MakersAsylumIndia/MAPone/datasheets/2EZ13D5-TP_sml.jpg

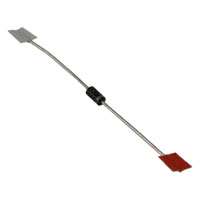
datasheets/2EZ13D5-TP_sml.jpg
