MakersAsylumIndia/MAPone/datasheets/9B-SERIES_sml.jpg

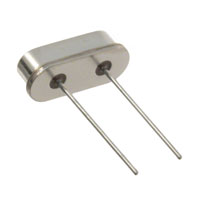
datasheets/9B-SERIES_sml.jpg
