MakersAsylumIndia/MAPone/datasheets/28-PDip_sml.jpg

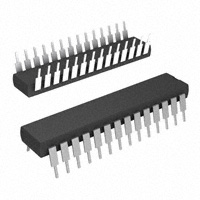
datasheets/28-PDip_sml.jpg
