MakersAsylumIndia/MAPone/datasheets/28-VFQFN Exposed Pad_sml.jpg

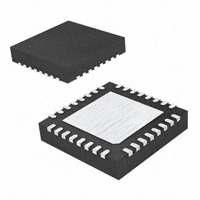
datasheets/28-VFQFN Exposed Pad_sml.jpg
