MakersAsylumIndia/MAPone/datasheets/67996-206hlf_sml.JPG

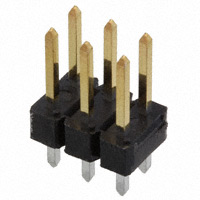
datasheets/67996-206hlf_sml.JPG
