MakersAsylumIndia/MAPone/datasheets/10118193-0001LF_sml.jpg

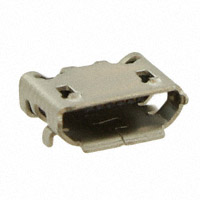
datasheets/10118193-0001LF_sml.jpg
