MakersAsylumIndia/MAPone/datasheets/CF Series 10k_sml.jpg

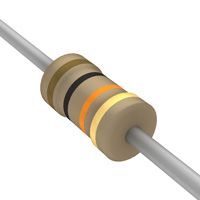
datasheets/CF Series 10k_sml.jpg
