MakersAsylumIndia/MAPone/datasheets/CL Series 0805(2012 Metric) 9_sml.jpg

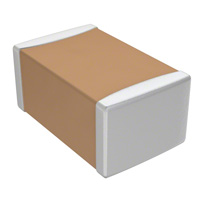
datasheets/CL Series 0805(2012 Metric) 9_sml.jpg
