MakersAsylumIndia/MAPone/datasheets/ED281DT_sml.JPG

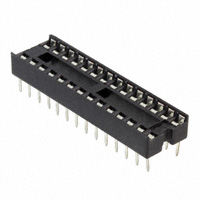
datasheets/ED281DT_sml.JPG
