MakersAsylumIndia/MAPone/datasheets/ERJ-0805 Pkg_sml.jpg

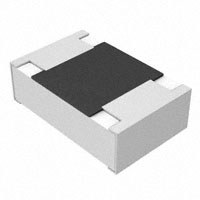
datasheets/ERJ-0805 Pkg_sml.jpg
