MakersAsylumIndia/MAPone/datasheets/ESK107M035AE3AA_sml.jpg

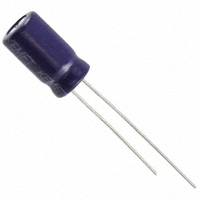
datasheets/ESK107M035AE3AA_sml.jpg
