MakersAsylumIndia/MAPone/datasheets/FSM4JH_sml.jpg

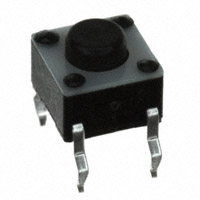
datasheets/FSM4JH_sml.jpg
