MakersAsylumIndia/MAPone/datasheets/LTST-C170YKT,LTST-C170CKT,LTST-C170AKT,LTST-C170EKT,LTST-C170GKT_sml.jpg

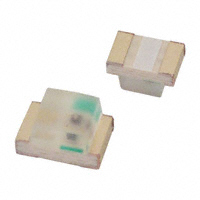
datasheets/LTST-C170YKT,LTST-C170CKT,LTST-C170AKT,LTST-C170EKT,LTST-C170GKT_sml.jpg
