MakersAsylumIndia/MAPone/datasheets/MFG_RMC SERIES_sml.jpg

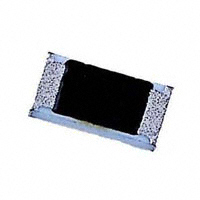
datasheets/MFG_RMC SERIES_sml.jpg
