MakersAsylumIndia/MAPone/datasheets/PJ-002A_sml.jpg

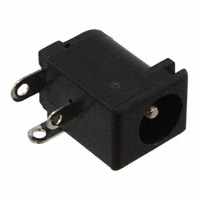
datasheets/PJ-002A_sml.jpg
