MakersAsylumIndia/MAPone/datasheets/PPPC061LGBN-RC_sml (1).jpg

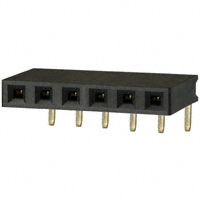
datasheets/PPPC061LGBN-RC_sml (1).jpg
