MakersAsylumIndia/MAPone/datasheets/PPTC061LFBN-RC_sml.jpg

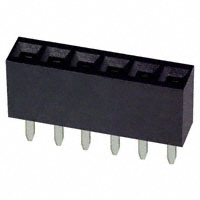
datasheets/PPTC061LFBN-RC_sml.jpg
