MakersAsylumIndia/MAPone/datasheets/PPTC081LFBN-RC_sml.jpg

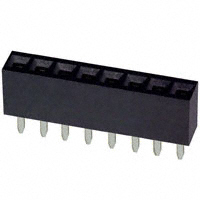
datasheets/PPTC081LFBN-RC_sml.jpg
