MakersAsylumIndia/MAPone/datasheets/PREC040SAAN-RC_sml.jpg

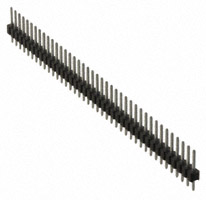
datasheets/PREC040SAAN-RC_sml.jpg
