MakersAsylumIndia/MAPone/datasheets/SOT-23-6 PKG_sml.jpg

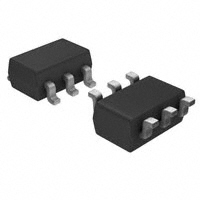
datasheets/SOT-23-6 PKG_sml.jpg
