MakersAsylumIndia/MAPone/datasheets/TO-220-3_sml.jpg

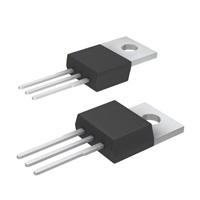
datasheets/TO-220-3_sml.jpg
