MakersAsylumIndia/MAPone/datasheets/WP710A10GD_sml.jpg

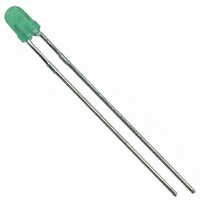
datasheets/WP710A10GD_sml.jpg
