MakersAsylumIndia/MAPone/images/DSC_0109.jpg

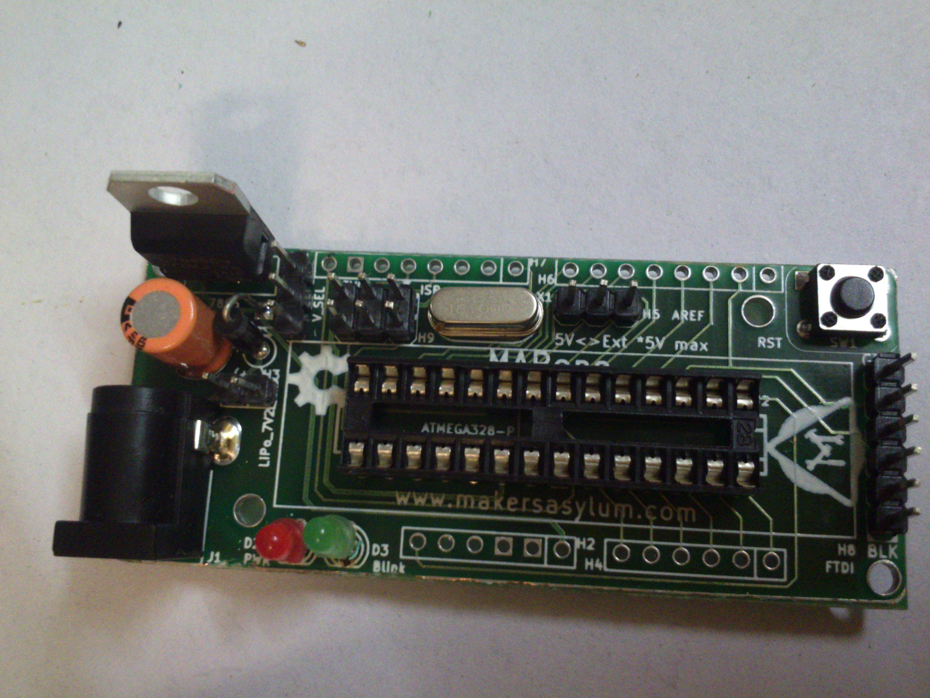
images/DSC_0109.jpg
