MakersAsylumIndia/MAPone/images/DSCN0591.JPG

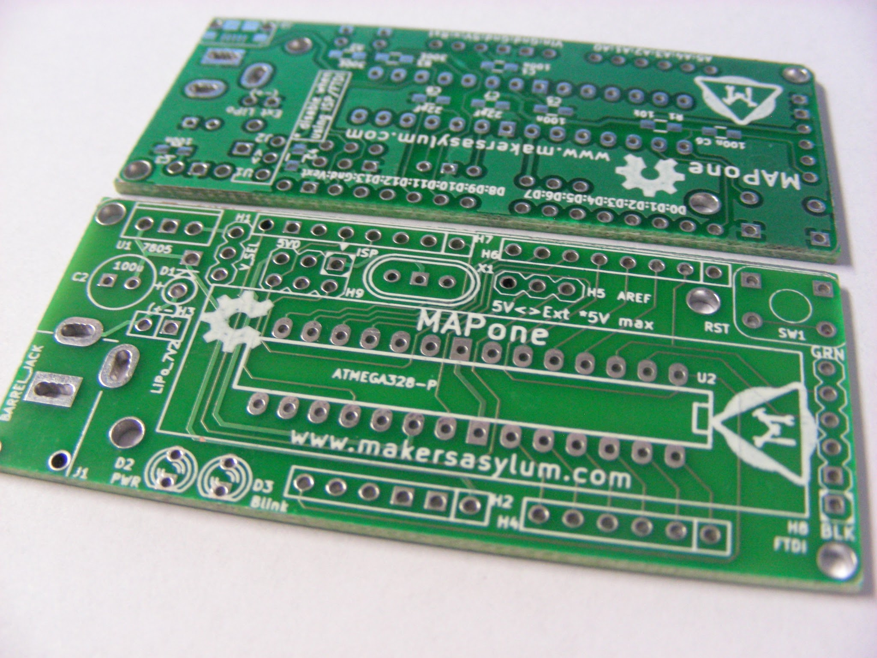
images/DSCN0591.JPG
