MakersAsylumIndia/MAPone/images/MAPone_01.png

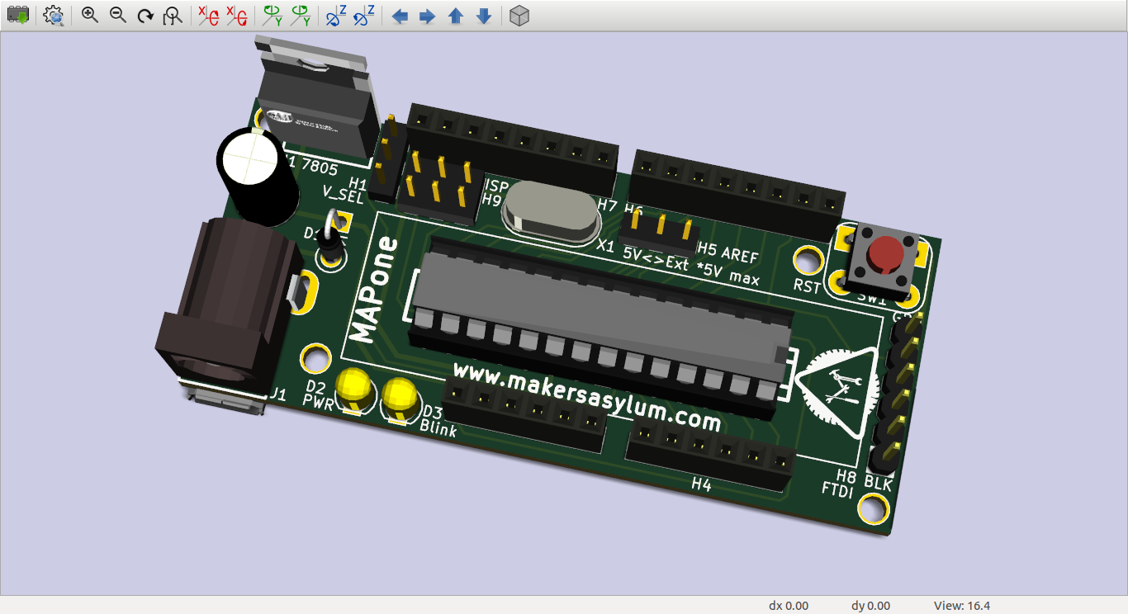
images/MAPone_01.png
