MakersAsylumIndia/MAPone/images/MAPone_02.png

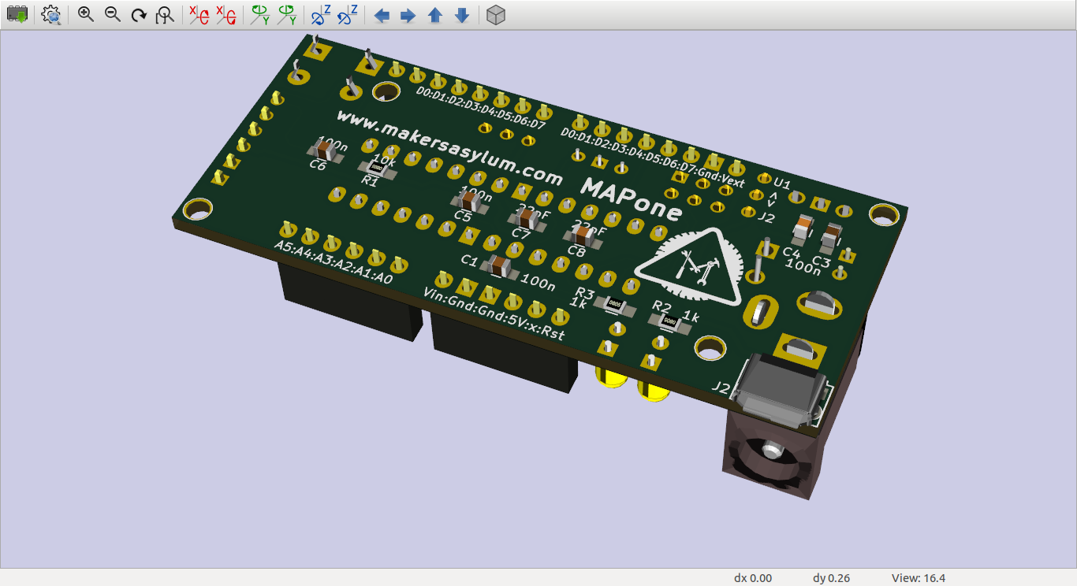
images/MAPone_02.png
