MakersAsylumIndia/MAPone/images/MAPone_03.png

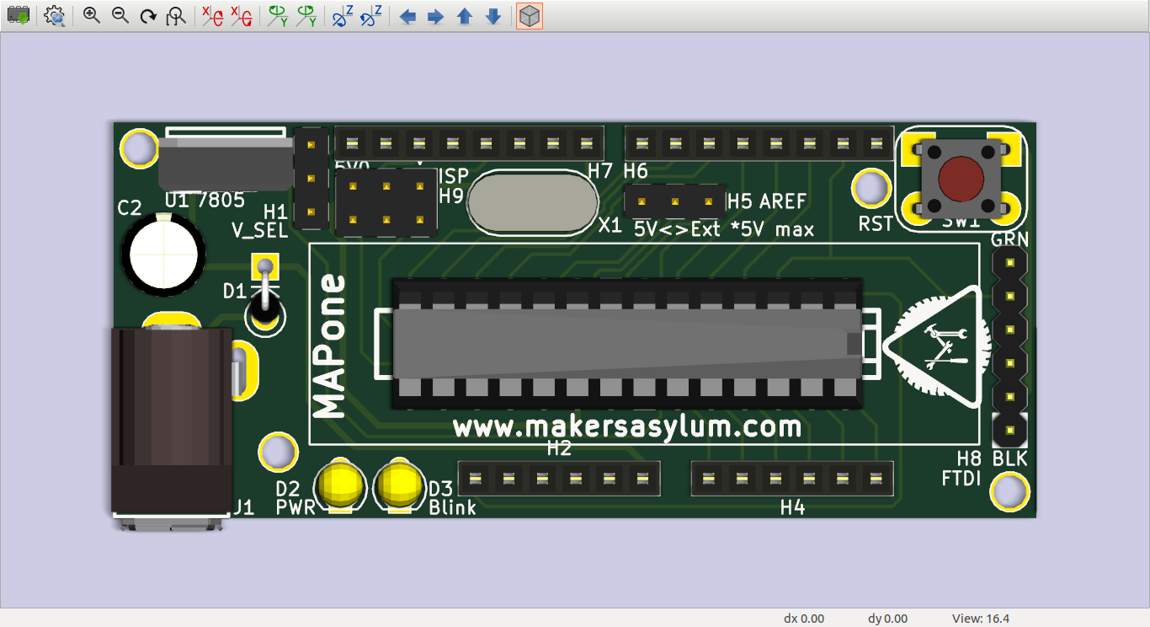
images/MAPone_03.png
