MakersAsylumIndia/MAPone/images/MAPone_04.png

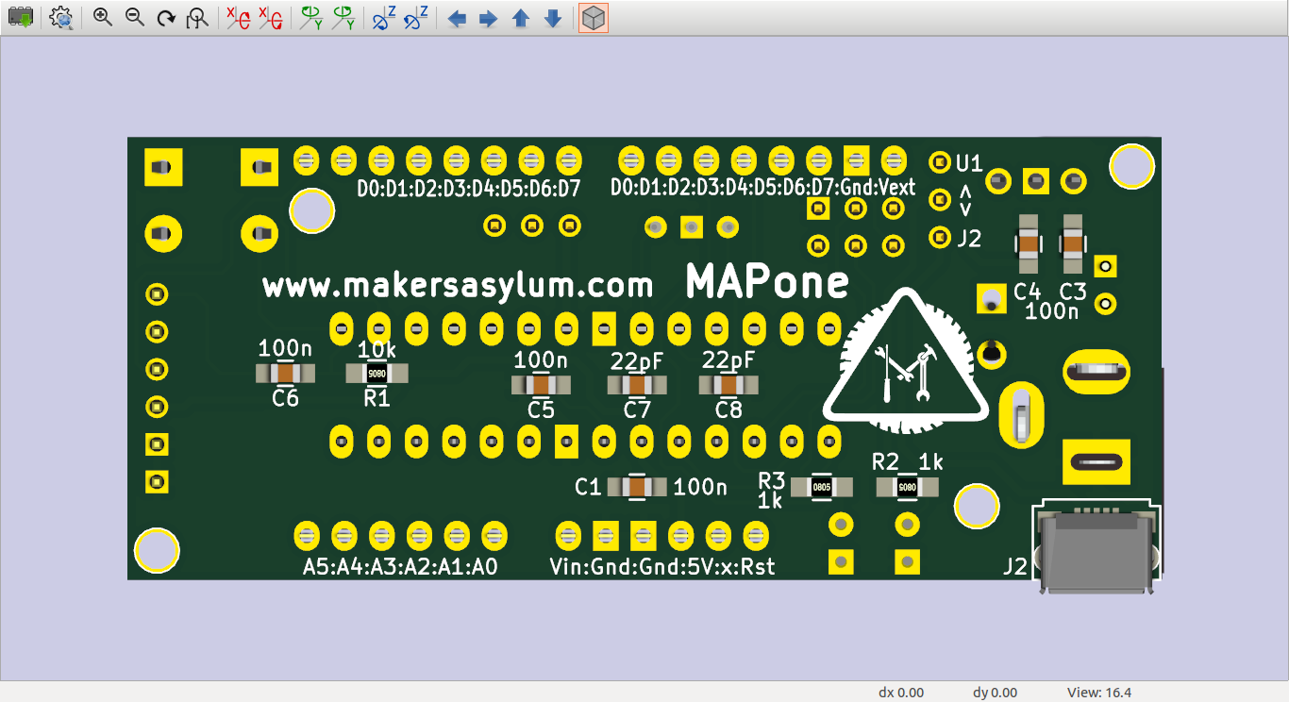
images/MAPone_04.png
