MakersAsylumIndia/MAPone/images/MAPone_08.png

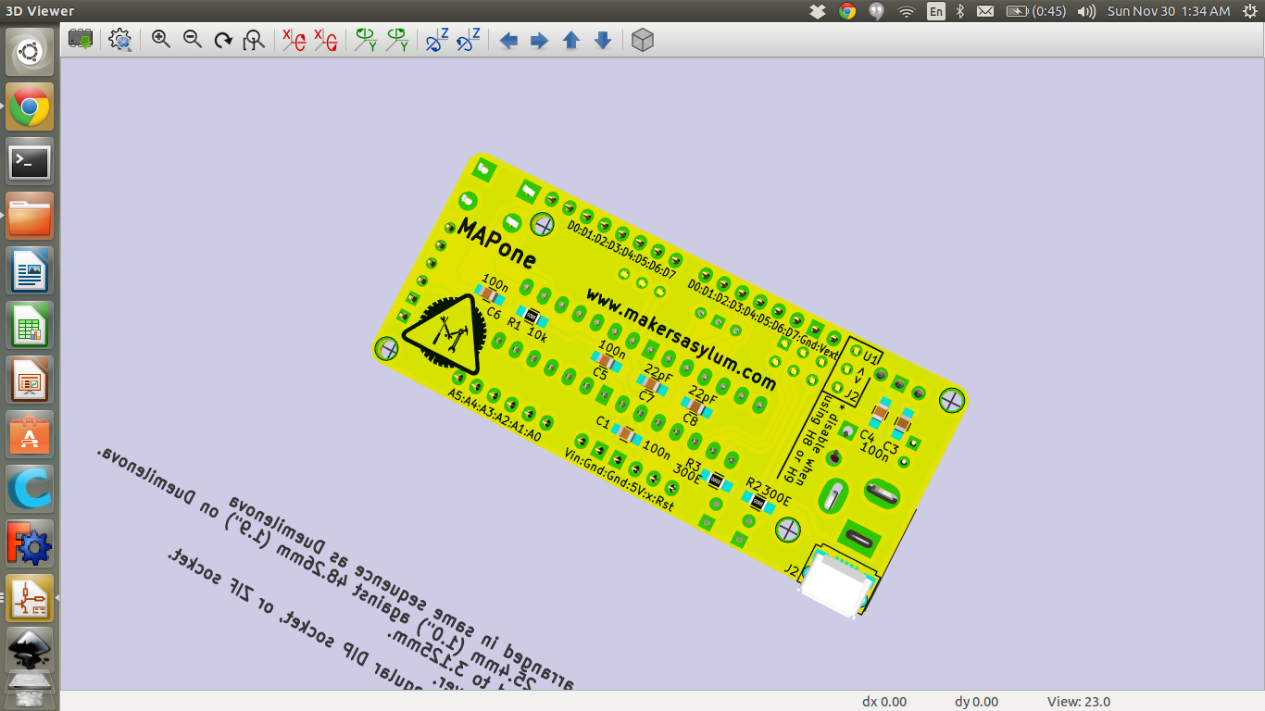
images/MAPone_08.png
