MakersAsylumIndia/MAPone/images/MAPone_09.png

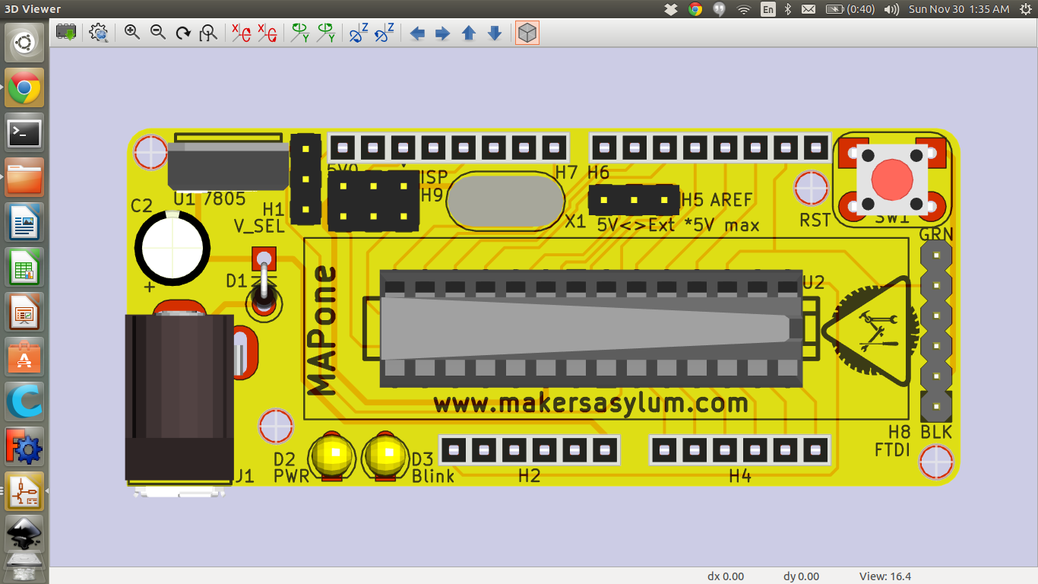
images/MAPone_09.png
