MakersAsylumIndia/MAPone/images/MAPone_10.png

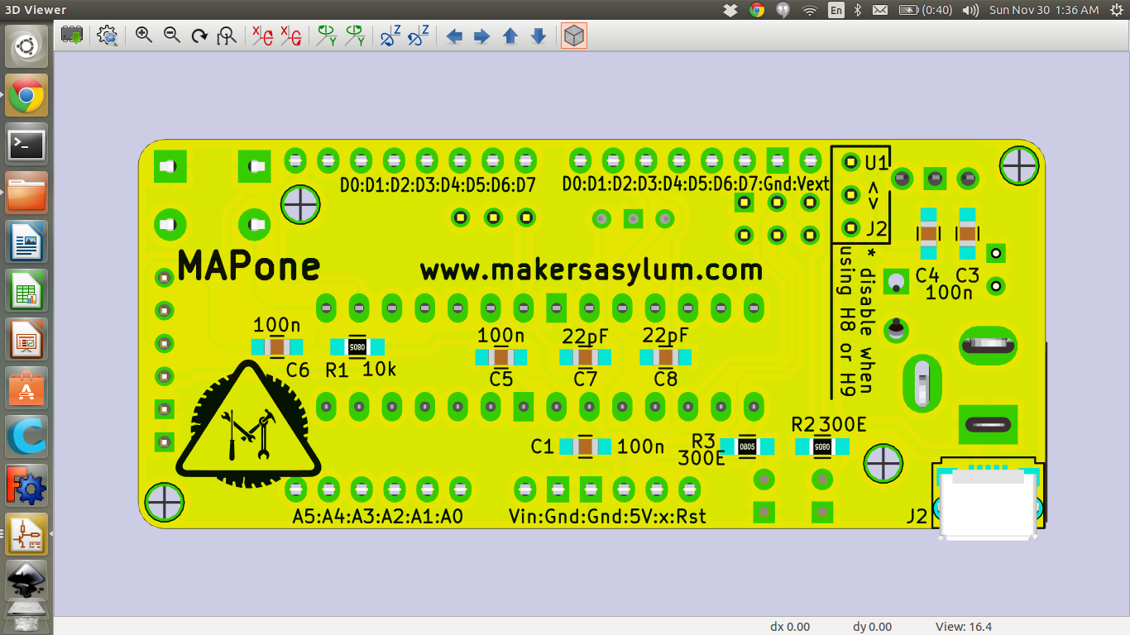
images/MAPone_10.png
