MakersAsylumIndia/MAPone/images/MAPone_13.png

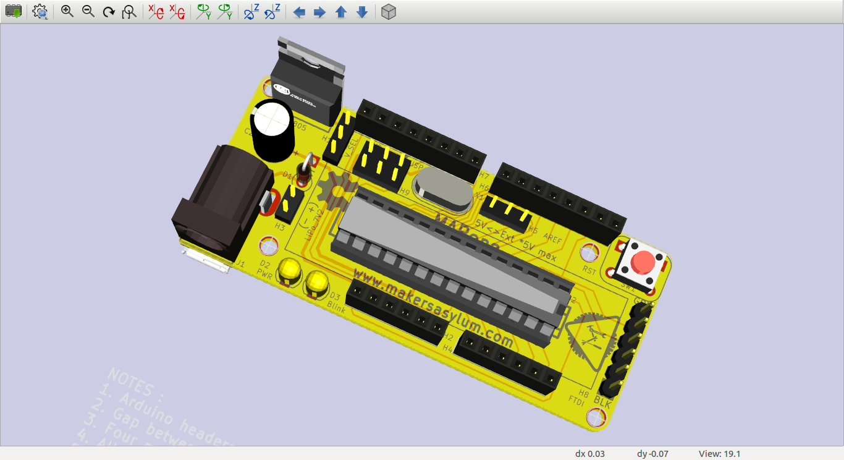
images/MAPone_13.png
