MakersAsylumIndia/MAPone/images/MAPone_14.png

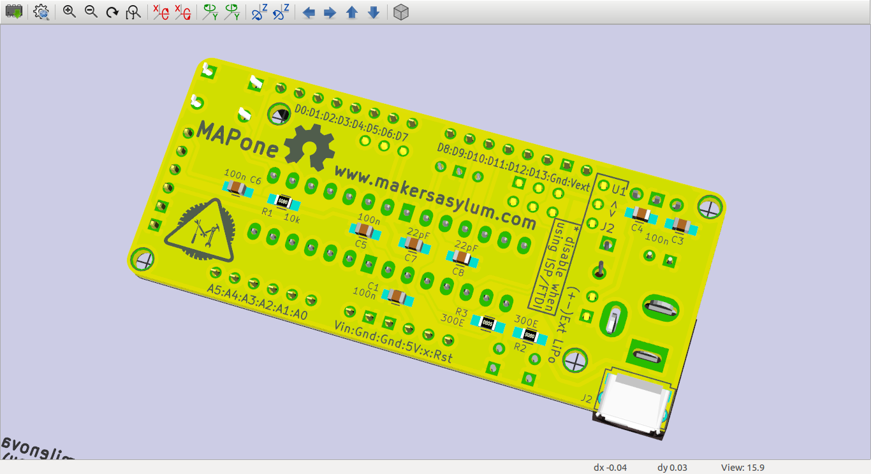
images/MAPone_14.png
