MakersAsylumIndia/MAPone/images/MAPone_15.png

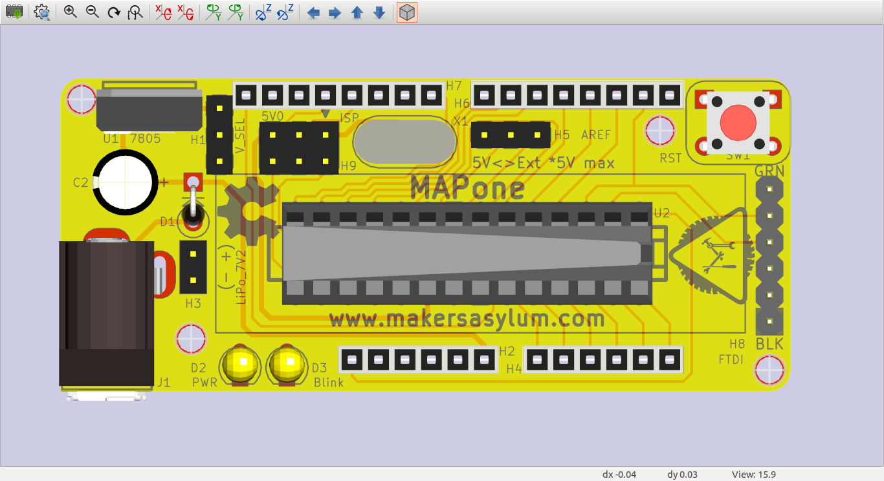
images/MAPone_15.png
