MakersAsylumIndia/MAPone/images/MAPone_16.png

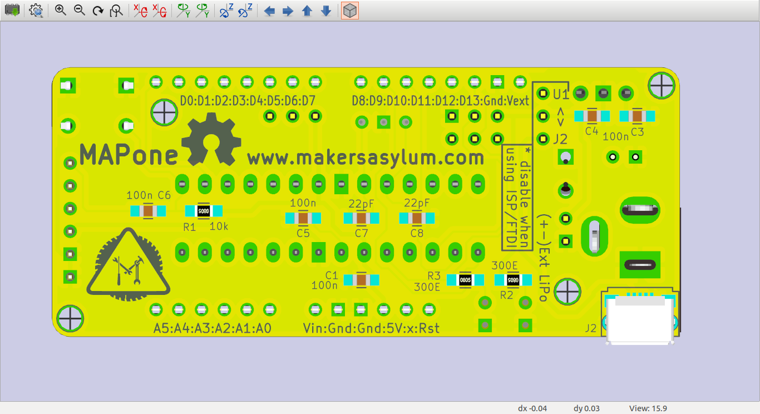
images/MAPone_16.png
