MakersAsylumIndia/MAPone/images/MAPone_18.png

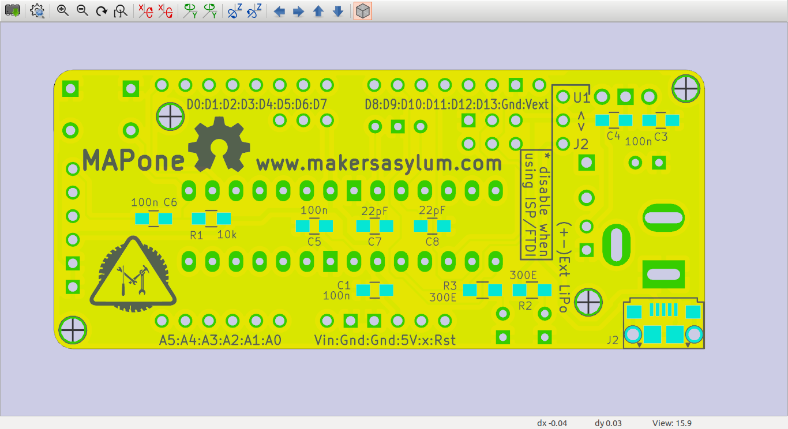
images/MAPone_18.png
