MakersAsylumIndia/MAPone/images/MAPone_19.png

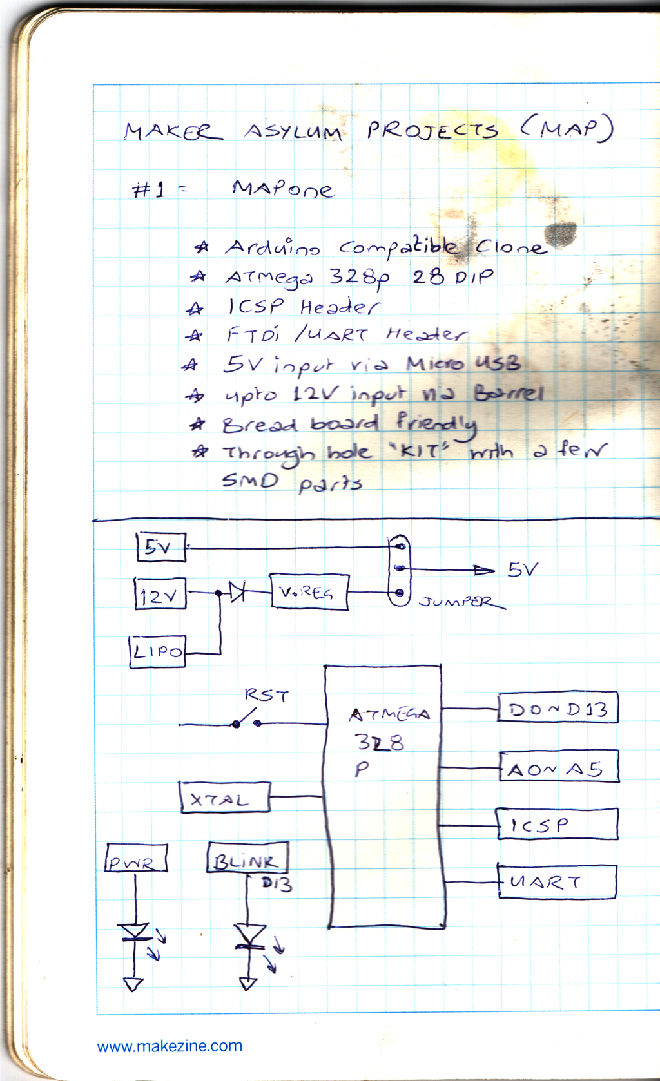
images/MAPone_19.png
