MakersAsylumIndia/MAPone/kicad/MAPone_assembly.png

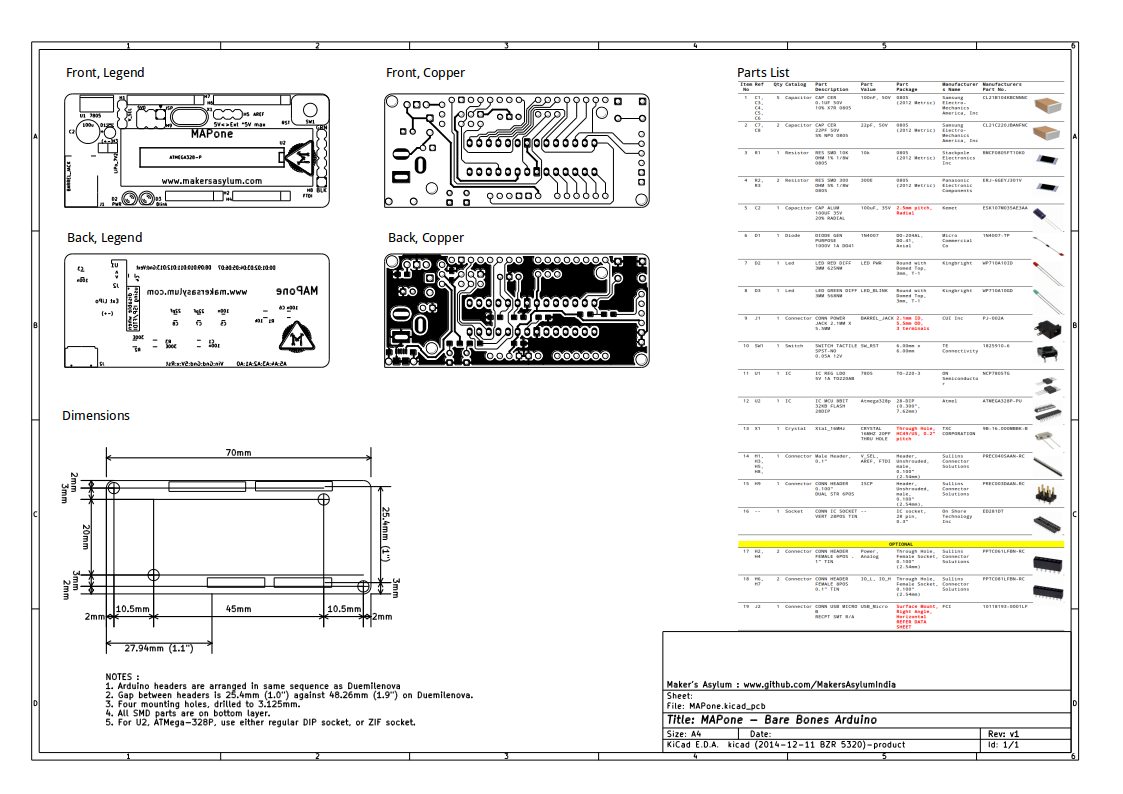
kicad/MAPone_assembly.png
