MakersAsylumIndia/MAPone/Eagle/USB-UART Bridge/UsbUartBridge.sch

## EAGLE design Eagle/USB-UART Bridge/UsbUartBridge.sch (2014-12-02)

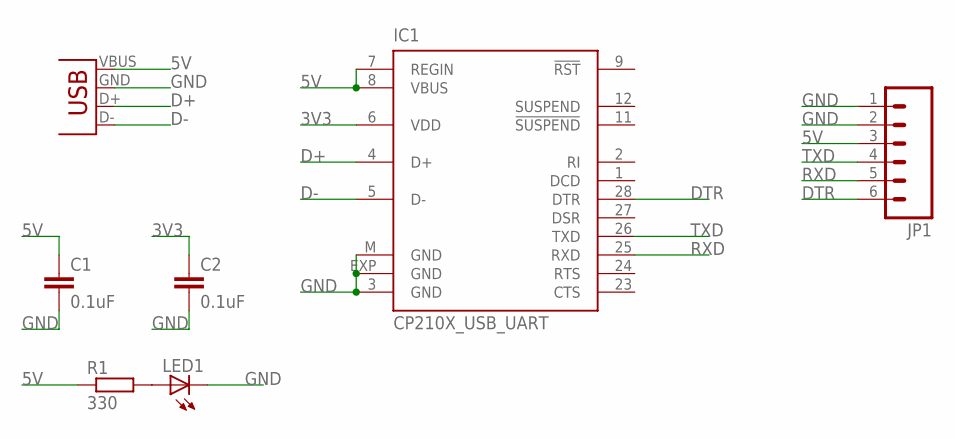
[picture p56: schematic UsbUartBridge.sch]

Parts:
C1, C2: 0.1uF; C025-024X044
IC1: CP210X_USB_UART; MLP28
JP1: M06SIP; 1X06
LED1: LED3MM
R1: 330; 0204/7
X1: USB-A-H

Connections:
3V3: C2.1, IC1.6 (VDD)
5V: C1.1, IC1.7 (REGIN), IC1.8 (VBUS), JP1.3, R1.1, X1.VBUS (GND)
D+: IC1.4 (D+), X1.D+ (D-)
D-: IC1.5 (D-), X1.D- (D+)
DTR: IC1.28 (DTR), JP1.6
GND: C1.2, C2.2, IC1.3 (GND), IC1.EXP (GND), IC1.M (GND), JP1.1, JP1.2, LED1.K (C), X1.GND (VBUS)
unnamed: LED1.A, R1.2
RXD: IC1.25 (RXD), JP1.5
TXD: IC1.26 (TXD), JP1.4
